Artyum/FPV-Headtracker/Images/DSC_3234.JPG

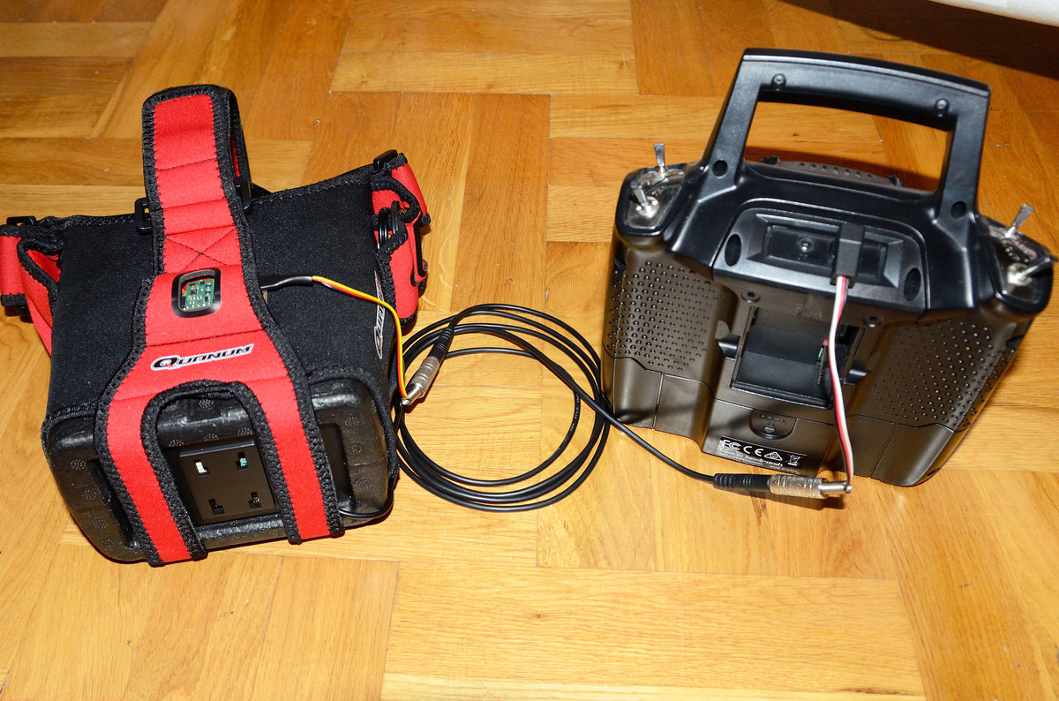
Images/DSC_3234.JPG
