Artyum/FPV-Headtracker/Images/DSC_3267.JPG

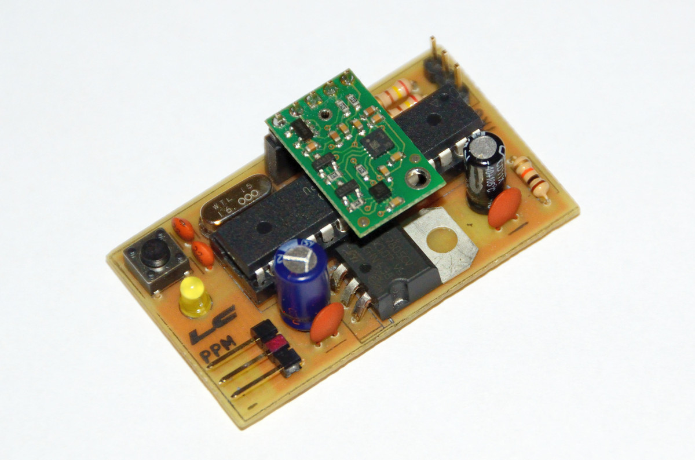
Images/DSC_3267.JPG
