Artyum/FPV-Headtracker/Images/FPVHT_Kicad1.jpg

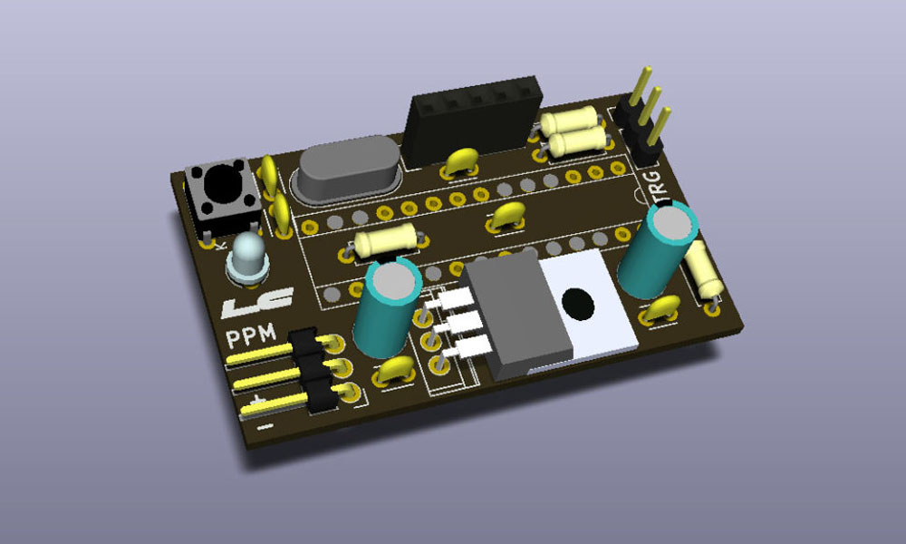
Images/FPVHT_Kicad1.jpg
