Artyum/FPV-Headtracker/Images/FPVHT_Kicad2.jpg

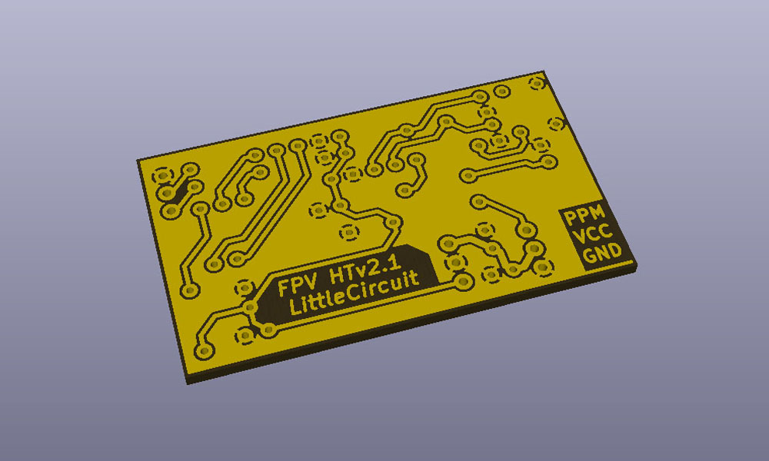
Images/FPVHT_Kicad2.jpg
